alexander0038/TDP-Robocup-Tux_3/Hardware/Chassis Pictures/Chassis_2.png

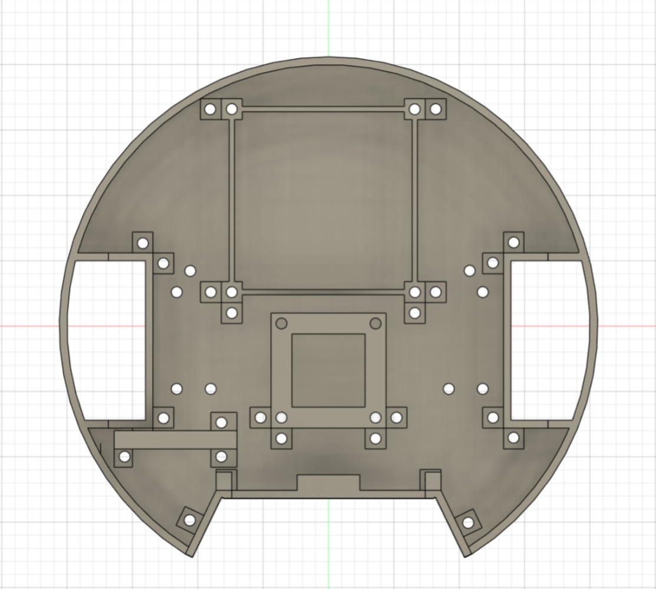
Hardware/Chassis Pictures/Chassis_2.png
