alexander0038/TDP-Robocup-Tux_3/Hardware/Chassis Pictures/Chassis_4.png

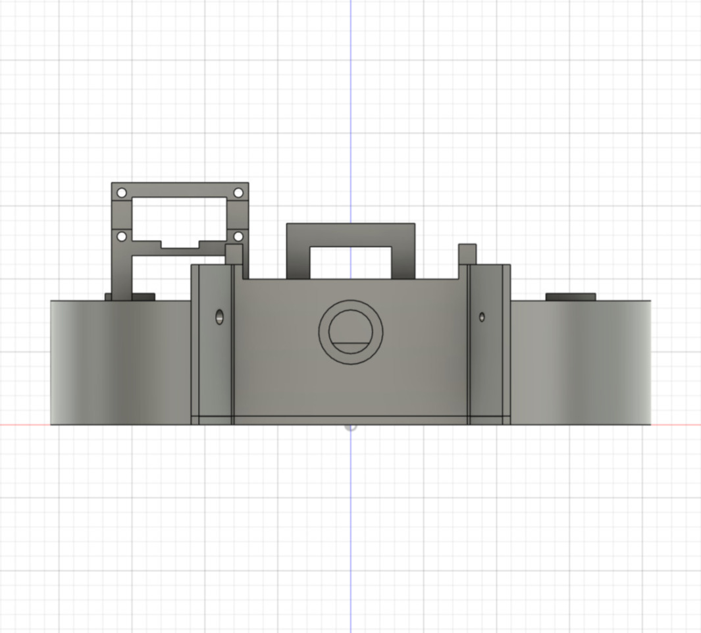
Hardware/Chassis Pictures/Chassis_4.png
