alexander0038/TDP-Robocup-Tux_3/Hardware/Robot pictures/Robot_picture_3.png

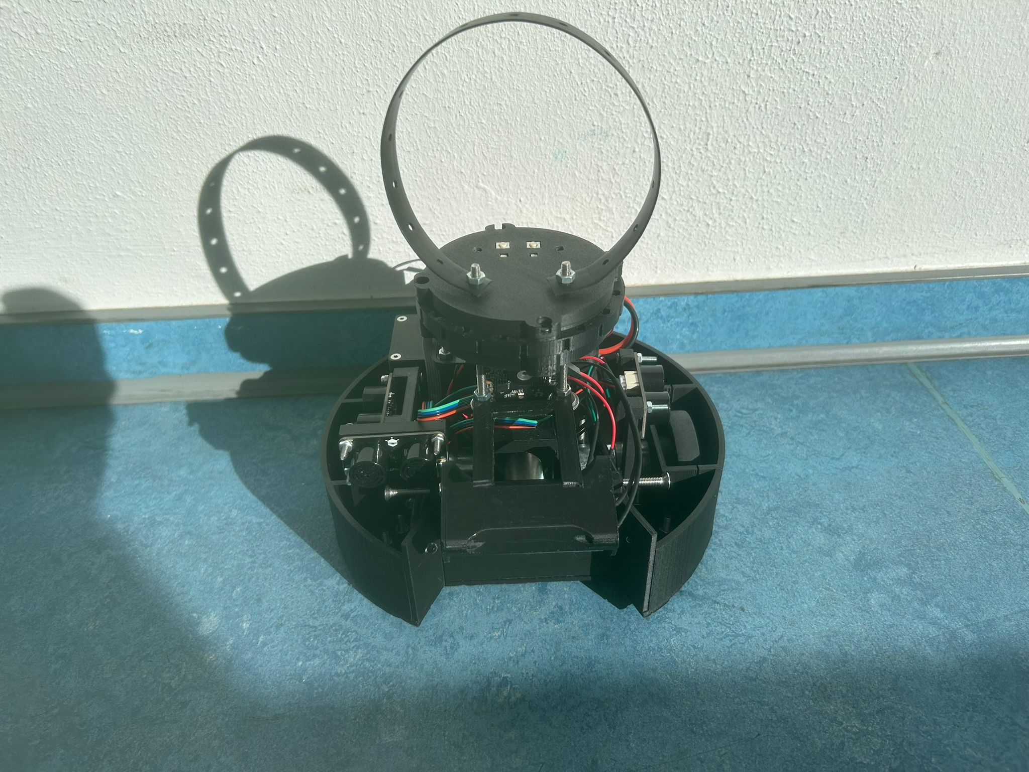
Hardware/Robot pictures/Robot_picture_3.png
