alexander0038/TDP-Robocup-Tux_3/software/FlowChart.png

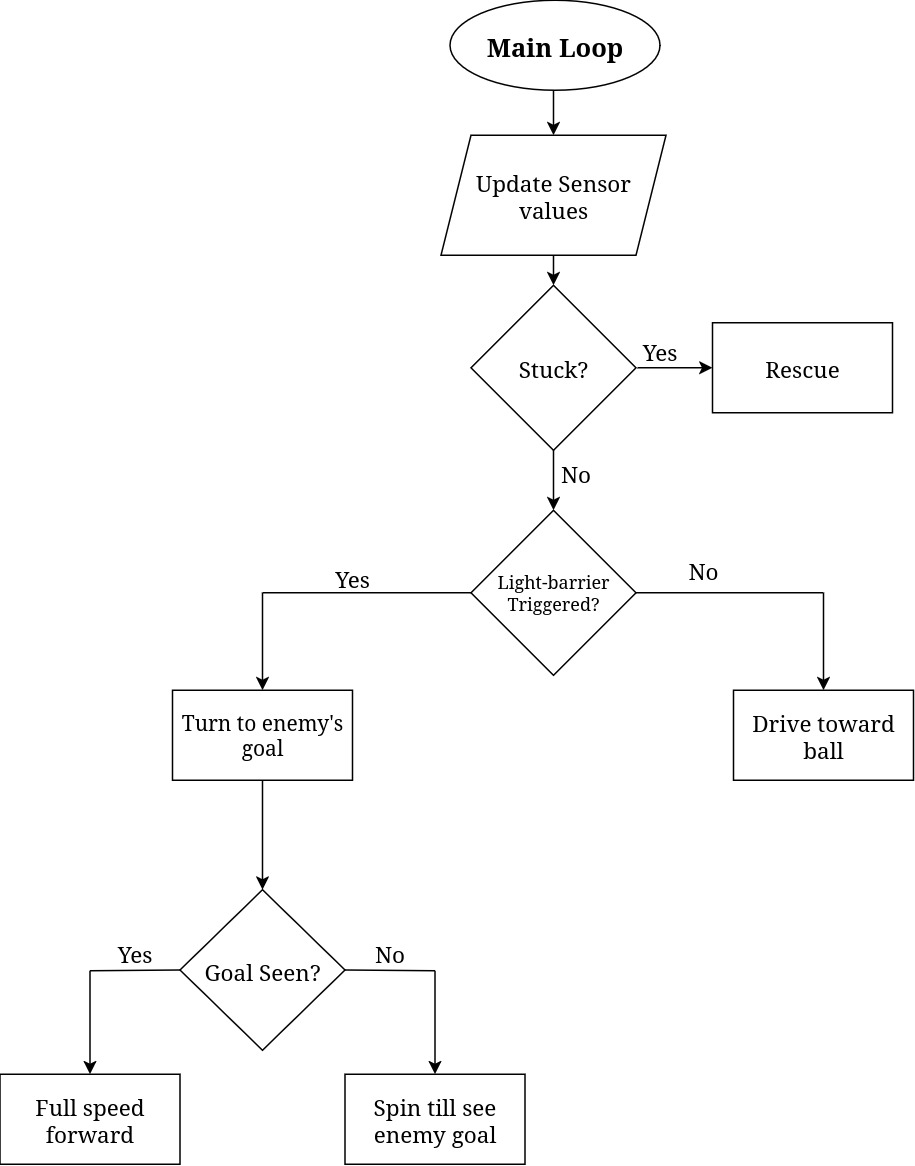
software/FlowChart.png
