alexander0038/TDP-Robocup-Tux_3/Tux_3.png

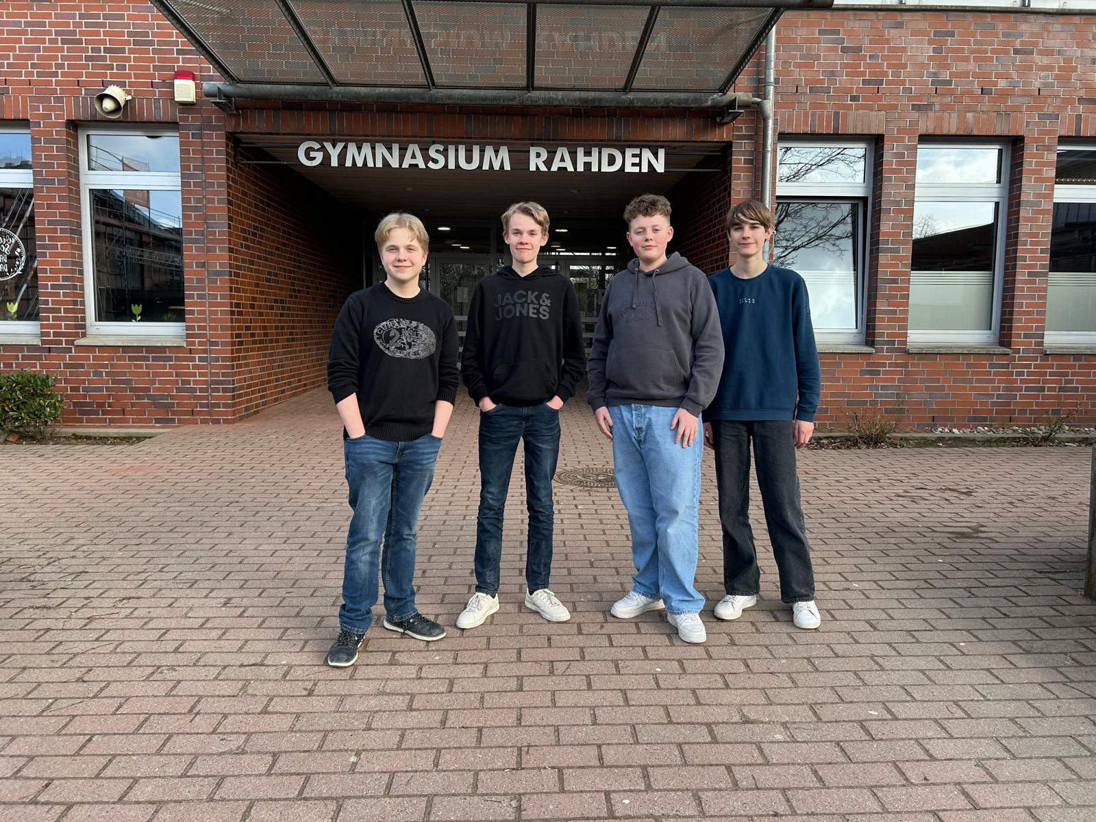
Tux_3.png
